Vishvak365/OpenCycle/pcb/symlib.py

"""Symbol pin lookup (KiCad 7 system libraries + the local pcb/lib/OpenCycle.kicad_sym)."""
import functools
from pathlib import Path

from kiutils.symbol import SymbolLib

LIB = "/usr/share/kicad/symbols/"
LOCAL = Path(__file__).parent / "lib"


def lib_path(name):
    local = LOCAL / f"{name}.kicad_sym"
    return str(local) if local.exists() else LIB + name + ".kicad_sym"


@functools.lru_cache(None)
def lib(name):
    return SymbolLib.from_file(lib_path(name))


def get(libname, sym):
    L = lib(libname)
    s = next(x for x in L.symbols if x.entryName == sym)
    if s.extends:
        base = next(x for x in L.symbols if x.entryName == s.extends)
        return s, base
    return s, s


def pins(libname, sym):
    s, base = get(libname, sym)
    out = []
    for u in base.units:
        for p in u.pins:
            out.append((p.number, p.name, p.electricalType, p.position.X, p.position.Y, p.position.angle or 0, p.length))
    return out
